granthussey/ultimate-pegboard-backing/scad/backing_2x1_grid_lite.scad

// === Pegboard Backing Grid Lite: 2x1 ===
// 2 columns, 1 row - grid pegs with corner hooks, lightweight

include <../pegboard_library.scad>

$fn = 64;

cols = 2;
rows = 1;

pegboard_backing_lite(cols, rows, "grid_corner_hooks");
